JeremyProffittOrg/kb2040-single-key/BigSwitchCase.scad

// BigSwitchCase
// Case for the Kailh Big Switch / Adafruit KB2040 single-key build.
// Generated from the Tinkercad STL export (Big Switch Single Case part1);
// mesh translated to an OpenSCAD polyhedron.
// 4250 vertices, 8512 triangular faces.
// Units: millimetres.
//
// Side note: square openings on opposite outer walls are the tab-release
// access holes — insert a small flat screwdriver to push the switch tabs
// inward and free the Kailh Big Switch from the base.

module big_switch_case() {
    mesh_vertices = [
        [-68, 115.97, 36.107],
        [-68, 115.988, 36.136],
        [-68, 152.9, 1.625],
        [-68, 115.945, 36.08],
        [-68, 115.915, 36.056],
        [-68, 115.879, 36.036],
        [-68, 115.839, 36.019],
        [-68, 115.795, 36.007],
        [-68, 115.749, 36],
        [-68, 115.702, 35.998],
        [-68, 110.298, 35.998],
        [-68, 115.97, 39.893],
        [-68, 115.945, 39.92],
        [-68, 152.9, 63.375],
        [-68, 115.795, 39.993],
        [-68, 115.839, 39.981],
        [-68, 115.879, 39.964],
        [-68, 115.915, 39.944],
        [-68, 115.999, 39.834],
        [-68, 115.988, 39.864],
        [-68, 116.002, 39.802],
        [-65.913, 103.858, 45.729],
        [-65.859, 103.998, 45.796],
        [-65.852, 103.871, 45.796],
        [-65.888, 103.722, 45.729],
        [-65.83, 103.748, 45.796],
        [-65.859, 122.002, 45.796],
        [-65.921, 122.002, 45.729],
        [-65.921, 103.998, 45.729],
        [-65.957, 103.849, 45.657],
        [-65.966, 103.998, 45.657],
        [-65.931, 103.704, 45.657],
        [-65.984, 103.843, 45.581],
        [-65.993, 103.998, 45.581],
        [-65.957, 103.692, 45.581],
        [-65.993, 122.002, 45.581],
        [-65.966, 103.689, 45.502],
        [-65.993, 103.841, 45.502],
        [-66.224, 71.051, 1.371],
        [-66.541, 71.127, 1.371],
        [-66.212, 71.127, 1.123],
        [-28.702, 140, 4.998],
        [-23.298, 155, 4.998],
        [-28.702, 155, 4.998],
        [-68, 110.055, 39.92],
        [-68, 73.1, 63.375],
        [-68, 110.085, 39.944],
        [-68, 110.03, 39.893],
        [-68, 110.012, 39.864],
        [-68, 110.001, 39.834],
        [0.601999, 86.179, 3.038],
        [0.636999, 86.181, 3.038],
        [0.601999, 86.398, 2.998],
        [-68, 109.997, 39.802],
        [-68, 109.997, 36.198],
        [0.67, 86.189, 3.038],
        [0.702, 86.202, 3.038],
        [-68, 110.001, 36.166],
        [-68, 110.012, 36.136],
        [-68, 73.1, 1.625],
        [-68, 110.03, 36.107],
        [16, 110.251, 40],
        [16, 110.298, 40.003],
        [16, 73.1, 63.375],
        [16, 115.749, 40],
        [16, 152.9, 63.375],
        [16, 115.702, 40.003],
        [-68, 110.121, 36.036],
        [-68, 110.161, 36.019],
        [16, 115.795, 39.993],
        [-68, 110.251, 36],
        [-68, 110.121, 39.964],
        [-68, 110.161, 39.981],
        [-68, 110.205, 39.993],
        [-65.306, 122.451, 36.052],
        [-65.252, 122.456, 36.052],
        [-65.252, 122.59, 36.093],
        [-68, 110.205, 36.007],
        [-68, 110.085, 36.056],
        [-68, 110.055, 36.08],
        [-65.289, 122.308, 36.022],
        [-68, 110.251, 40],
        [16, 110.205, 36.007],
        [16, 73.1, 1.625],
        [16, 110.251, 36],
        [-65.324, 122.296, 36.022],
        [-65.358, 122.434, 36.052],
        [-29.003, 155, 5.198],
        [-29.003, 155, 8.802],
        [-29.003, 140, 8.802],
        [-65.252, 122.311, 36.022],
        [-65.493, 103.677, 45.948],
        [-65.416, 103.779, 45.978],
        [-65.452, 103.63, 45.948],
        [-35.5, 141.002, 39],
        [-16.5, 140.075, 39],
        [-16.5, 141.002, 39],
        [16, 115.988, 36.136],
        [16, 152.9, 1.625],
        [16, 115.999, 36.166],
        [16, 115.97, 36.107],
        [-65.564, 103.582, 45.907],
        [-65.528, 103.731, 45.948],
        [16, 115.945, 36.08],
        [16, 115.915, 36.056],
        [16, 115.879, 36.036],
        [-65.321, 122.583, 36.093],
        [0.601999, 141.002, 39.998],
        [-52.602, 141.002, 39.998],
        [-68, 115.702, 40.003],
        [16, 116.002, 36.198],
        [-35.5, 140.075, 39],
        [16, 115.988, 39.864],
        [16, 115.999, 39.834],
        [16, 116.002, 39.802],
        [16, 115.945, 39.92],
        [16, 115.915, 39.944],
        [16, 115.879, 39.964],
        [-65.609, 103.652, 45.907],
        [16, 115.839, 39.981],
        [-65.44, 103.816, 45.978],
        [16, 115.97, 39.893],
        [16, 110.03, 36.107],
        [16, 110.012, 36.136],
        [-66.517, 71.201, 1.123],
        [-66.478, 71.32, 0.887],
        [-66.193, 71.252, 0.887],
        [-65.389, 103.748, 45.978],
        [-65.407, 103.593, 45.948],
        [-66.807, 71.32, 1.123],
        [-16.273, 141.002, 38.896],
        [-16.345, 141.002, 38.954],
        [-16.422, 141.002, 38.988],
        [-65.556, 103.792, 45.948],
        [-65.645, 103.731, 45.907],
        [16, 110.298, 35.998],
        [16, 115.702, 35.998],
        [16, 115.749, 36],
        [16, 115.795, 36.007],
        [16, 115.839, 36.019],
        [13.757, 122.221, 36.144],
        [13.776, 122.113, 36.144],
        [13.852, 122.129, 36.204],
        [-65.681, 122.574, 36.204],
        [-65.645, 122.723, 36.271],
        [-65.725, 122.632, 36.271],
        [13.783, 122.002, 36.144],
        [13.688, 122.094, 36.093],
        [-16.345, 140.075, 38.954],
        [-16.273, 140.075, 38.896],
        [16, 110.055, 39.92],
        [16, 110.03, 39.893],
        [16, 110.205, 39.993],
        [16, 110.161, 39.981],
        [16, 110.121, 39.964],
        [16, 110.085, 39.944],
        [-66.166, 71.422, 0.67],
        [-65.9, 71.229, 0.887],
        [-16.054, 141.002, 38.481],
        [-16.095, 141.002, 38.608],
        [16, 109.997, 36.198],
        [-16.146, 141.002, 38.722],
        [-65.793, 122.526, 36.271],
        [-65.757, 122.675, 36.343],
        [-65.83, 122.561, 36.343],
        [13.859, 122.002, 36.204],
        [13.921, 122.002, 36.271],
        [13.912, 122.142, 36.271],
        [13.83, 122.252, 36.204],
        [0.731001, 86.22, 3.038],
        [0.757, 86.243, 3.038],
        [-65.672, 122.772, 36.343],
        [0.780001, 86.269, 3.038],
        [0.798, 86.298, 3.038],
        [0.811001, 86.33, 3.038],
        [0.819, 86.363, 3.038],
        [-65.347, 103.906, 45.996],
        [0.820999, 86.398, 3.038],
        [-65.289, 103.692, 45.978],
        [-65.324, 103.704, 45.978],
        [-65.289, 103.849, 45.996],
        [-65.9, 152.9, 65],
        [-64.199, 151.63, 65],
        [-63.938, 151.79, 65],
        [-65.776, 122.701, 36.419],
        [-65.852, 122.583, 36.419],
        [-64.431, 151.431, 65],
        [13.993, 122.002, 36.419],
        [13.957, 122.151, 36.343],
        [13.966, 122.002, 36.343],
        [-63.052, 152.003, 65],
        [-63.357, 151.978, 65],
        [-63.655, 151.907, 65],
        [-65.358, 103.722, 45.978],
        [-65.358, 103.566, 45.948],
        [-65.9, 155, 1.625],
        [-65.335, 103.887, 45.996],
        [-65.321, 103.871, 45.996],
        [0.799, 86.012, 3.158],
        [0.857, 86.048, 3.158],
        [13.725, 122.323, 36.144],
        [13.793, 122.37, 36.204],
        [0.908001, 86.092, 3.158],
        [-65.003, 75.948, 65],
        [-65.003, 150.052, 65],
        [-64.978, 150.357, 65],
        [-64.63, 151.199, 65],
        [-64.79, 150.938, 65],
        [-65.306, 103.858, 45.996],
        [-64.907, 150.655, 65],
        [-64.63, 74.801, 65],
        [-64.79, 75.062, 65],
        [-65.9, 73.1, 65],
        [13.848, 122.407, 36.271],
        [13.743, 122.478, 36.204],
        [-64.907, 75.345, 65],
        [-64.978, 75.643, 65],
        [-16.347, 140.071, 38.954],
        [-64.431, 74.569, 65],
        [-64.199, 74.37, 65],
        [-63.938, 74.21, 65],
        [0.67, 85.97, 3.158],
        [-63.655, 74.093, 65],
        [0.736, 85.986, 3.158],
        [-16.284, 140.064, 38.896],
        [-16.353, 140.068, 38.954],
        [-16.362, 140.064, 38.954],
        [-65.473, 103.902, 45.978],
        [-65.459, 103.857, 45.978],
        [-65.688, 122.802, 36.419],
        [-16.375, 140.061, 38.954],
        [-16.437, 140.068, 38.988],
        [-16.391, 140.059, 38.954],
        [-65.576, 103.857, 45.948],
        [13.888, 122.278, 36.271],
        [-65.593, 103.998, 45.948],
        [-65.589, 103.927, 45.948],
        [-65.688, 103.906, 45.907],
        [11.052, 73.997, 65],
        [-63.052, 73.997, 65],
        [13.9, 73.1, 65],
        [-16.422, 140.075, 38.988],
        [0.601999, 85.965, 3.158],
        [-63.357, 74.022, 65],
        [16, 110.012, 39.864],
        [16, 110.001, 39.834],
        [16, 110.001, 36.166],
        [16, 110.055, 36.08],
        [16, 110.121, 36.036],
        [16, 110.161, 36.019],
        [16, 110.085, 36.056],
        [-65.783, 122.71, 36.498],
        [-65.913, 122.451, 36.419],
        [-65.859, 122.59, 36.498],
        [13.931, 122.296, 36.343],
        [-65.484, 103.998, 45.978],
        [13.888, 122.434, 36.343],
        [0.799, 85.793, 3.354],
        [-16.464, 140.065, 38.988],
        [-16.476, 140.064, 38.988],
        [-16.43, 140.054, 38.954],
        [0.702, 85.77, 3.354],
        [0.891001, 85.831, 3.354],
        [-65.593, 122.893, 36.498],
        [-65.693, 122.811, 36.498],
        [-65.357, 103.927, 45.996],
        [16, 109.997, 39.802],
        [-16.423, 140.073, 38.988],
        [-16.43, 140.07, 38.988],
        [-36, 85.762, 3.354],
        [-36, 85.575, 3.623],
        [-36, 85.925, 3.19662],
        [-16.426, 140.071, 38.988],
        [-16.445, 140.067, 38.988],
        [-65.416, 122.675, 36.144],
        [-65.389, 122.561, 36.093],
        [-65.335, 122.701, 36.144],
        [-16.454, 140.066, 38.988],
        [-65.493, 122.632, 36.144],
        [-65.452, 122.526, 36.093],
        [0.601999, 85.762, 3.354],
        [-16.409, 140.056, 38.954],
        [-16.488, 140.063, 38.988],
        [-16.476, 140.052, 38.954],
        [-16.452, 140.053, 38.954],
        [-36, 85.15, 4.786],
        [-36, 85.265, 4.348],
        [-36, 85.408, 3.957],
        [-66.166, 154.578, 64.33],
        [-66.132, 154.367, 64.524],
        [-65.9, 154.385, 64.524],
        [-16.367, 140.047, 38.896],
        [-36, 84.997, 6.273],
        [-36, 85.015, 5.76],
        [-36, 85.066, 5.261],
        [-36, 85.925, 38.05],
        [-65.564, 122.574, 36.144],
        [-65.528, 122.723, 36.204],
        [-36, 84.997, 38.05],
        [-65.609, 122.657, 36.204],
        [-65.44, 122.772, 36.204],
        [0.976, 85.883, 3.354],
        [1.052, 85.948, 3.354],
        [1.117, 86.024, 3.354],
        [-65.556, 122.796, 36.271],
        [-16.339, 140.051, 38.896],
        [1.169, 86.109, 3.354],
        [0.952, 86.143, 3.158],
        [-65.347, 122.802, 36.204],
        [-16.146, 140.075, 38.722],
        [-16.206, 140.075, 38.819],
        [-16.21, 140.068, 38.819],
        [-16.276, 140.07, 38.896],
        [1.014, 86.264, 3.158],
        [1.23, 86.298, 3.354],
        [1.03, 86.33, 3.158],
        [1.238, 86.398, 3.354],
        [1.035, 86.398, 3.158],
        [-66.195, 153.807, 64.823],
        [-66.333, 153.749, 64.823],
        [-66.101, 153.517, 64.92],
        [-16.206, 141.002, 38.819],
        [-36, 141.002, 6.273],
        [-36, 140.075, 38.05],
        [-36, 141.002, 38.05],
        [-65.9, 154.134, 64.69],
        [-66.093, 154.119, 64.69],
        [-65.9, 153.853, 64.823],
        [-65.364, 103.949, 45.996],
        [-36, 140.075, 3.19662],
        [-16.151, 140.067, 38.722],
        [-36, 140.985, 5.76],
        [-16.22, 140.061, 38.819],
        [0.988001, 86.201, 3.158],
        [1.207, 86.201, 3.354],
        [-66.049, 153.842, 64.823],
        [-65.9, 153.549, 64.92],
        [-66.002, 153.541, 64.92],
        [12.199, 151.63, 65],
        [13.9, 152.9, 65],
        [11.938, 151.79, 65],
        [-66.281, 154.074, 64.69],
        [12.63, 151.199, 65],
        [12.431, 151.431, 65],
        [-36, 140.425, 3.623],
        [-36, 140.238, 3.354],
        [-36, 140.592, 3.957],
        [-36, 140.735, 4.348],
        [-36, 140.85, 4.786],
        [-36, 140.934, 5.261],
        [-16.185, 140.051, 38.722],
        [-16.115, 140.056, 38.608],
        [-16.164, 140.059, 38.722],
        [-16.214, 140.044, 38.722],
        [-16.14, 140.047, 38.608],
        [12.79, 150.938, 65],
        [13.003, 150.052, 65],
        [12.978, 150.357, 65],
        [12.907, 150.655, 65],
        [-65.9, 154.974, 63.629],
        [-65.9, 155, 63.375],
        [-66.229, 154.974, 63.375],
        [11.357, 151.978, 65],
        [11.655, 151.907, 65],
        [11.052, 152.003, 65],
        [-16.298, 140.06, 38.896],
        [13.984, 122.157, 36.419],
        [-29.003, 71, 5.198],
        [-65.9, 71, 1.625],
        [-28.999, 71, 5.166],
        [-16.316, 140.055, 38.896],
        [-28.988, 71, 5.136],
        [-28.97, 71, 5.107],
        [-28.879, 71, 5.036],
        [-28.915, 71, 5.056],
        [-28.795, 71, 5.007],
        [-28.839, 71, 5.019],
        [1.403, 85.816, 3.957],
        [1.268, 85.914, 3.623],
        [1.184, 85.816, 3.623],
        [-16.1, 140.066, 38.608],
        [13.957, 122.308, 36.419],
        [-28.879, 71, 8.964],
        [-65.9, 71, 63.375],
        [-28.915, 71, 8.944],
        [13.9, 71, 63.375],
        [-28.702, 71, 9.003],
        [13.912, 122.451, 36.419],
        [13.966, 122.311, 36.498],
        [13.921, 122.456, 36.498],
        [-28.749, 71, 9],
        [-28.97, 71, 8.893],
        [-28.945, 71, 8.92],
        [-28.795, 71, 8.993],
        [1.385, 86.143, 3.623],
        [-28.839, 71, 8.981],
        [1.415, 86.269, 3.623],
        [15.771, 153.853, 63.375],
        [15.873, 153.541, 63.629],
        [15.897, 153.549, 63.375],
        [-16.238, 140.055, 38.819],
        [-23.03, 71, 5.107],
        [13.9, 71, 1.625],
        [-23.012, 71, 5.136],
        [15.799, 153.517, 63.877],
        [15.748, 153.193, 64.113],
        [15.873, 153.212, 63.877],
        [-23.085, 71, 5.056],
        [-23.055, 71, 5.08],
        [13.993, 122.159, 36.498],
        [15.771, 152.9, 64.113],
        [15.897, 152.9, 63.877],
        [1.336, 86.024, 3.623],
        [-23.121, 71, 5.036],
        [-23.161, 71, 5.019],
        [-23.121, 71, 8.964],
        [-23.161, 71, 8.981],
        [15.949, 153.224, 63.629],
        [14.003, 122.002, 36.498],
        [15.974, 152.9, 63.629],
        [-22.998, 71, 8.802],
        [-23.001, 71, 8.834],
        [-23.03, 71, 8.893],
        [-23.055, 71, 8.92],
        [-23.085, 71, 8.944],
        [-23.205, 71, 8.993],
        [15.974, 153.229, 63.375],
        [1.086, 85.732, 3.623],
        [-23.298, 71, 9.003],
        [-23.251, 71, 9],
        [0.976, 85.664, 3.623],
        [1.184, 85.597, 3.957],
        [-28.945, 71, 5.08],
        [-28.749, 71, 5],
        [-28.702, 71, 4.998],
        [-23.298, 71, 4.998],
        [-23.205, 71, 5.007],
        [-23.251, 71, 5],
        [-23.001, 71, 5.166],
        [-16.327, 140.039, 38.819],
        [-23.012, 71, 8.864],
        [-22.998, 71, 5.198],
        [-16.262, 140.049, 38.819],
        [-16.292, 140.044, 38.819],
        [-65.576, 122.85, 36.343],
        [-29.003, 71, 8.802],
        [-28.999, 71, 8.834],
        [-28.988, 71, 8.864],
        [-65.459, 122.85, 36.271],
        [-65.252, 103.689, 45.978],
        [-65.271, 103.843, 45.996],
        [-65.252, 103.841, 45.996],
        [-16.43, 140.043, 38.896],
        [-16.464, 140.041, 38.896],
        [1.302, 85.698, 3.957],
        [-65.481, 103.949, 45.978],
        [-65.368, 103.973, 45.996],
        [-16.5, 140.031, 38.819],
        [-16.454, 140.031, 38.819],
        [13.252, 122.59, 36.093],
        [13.321, 122.583, 36.093],
        [13.335, 122.701, 36.144],
        [-65.473, 122.907, 36.343],
        [-16.397, 140.045, 38.896],
        [-65.589, 122.883, 36.419],
        [1.425, 86.398, 3.623],
        [13.252, 122.71, 36.144],
        [-16.367, 140.036, 38.819],
        [-16.292, 140.032, 38.722],
        [13.389, 122.561, 36.093],
        [13.452, 122.526, 36.093],
        [13.493, 122.632, 36.144],
        [13.416, 122.675, 36.144],
        [-16.409, 140.033, 38.819],
        [-65.364, 122.942, 36.343],
        [1.485, 85.948, 3.957],
        [1.544, 86.092, 3.957],
        [13.44, 122.772, 36.204],
        [-16.339, 140.028, 38.722],
        [1.58, 86.243, 3.957],
        [1.592, 86.398, 3.957],
        [-16.445, 140.023, 38.722],
        [-16.391, 140.025, 38.722],
        [-65.252, 103.998, 46.003],
        [12.431, 74.569, 65],
        [12.63, 74.801, 65],
        [12.79, 75.062, 65],
        [-65.357, 122.883, 36.271],
        [12.907, 75.345, 65],
        [13.003, 75.948, 65],
        [12.978, 75.643, 65],
        [-16.25, 140.037, 38.722],
        [-65.252, 122.71, 36.144],
        [-65.252, 122.811, 36.204],
        [-65.252, 122.954, 36.343],
        [1.721, 86.22, 4.348],
        [-65.252, 122.893, 36.271],
        [11.357, 74.022, 65],
        [11.655, 74.093, 65],
        [1.735, 86.398, 4.348],
        [-16.316, 140.021, 38.608],
        [11.938, 74.21, 65],
        [12.199, 74.37, 65],
        [-65.481, 122.942, 36.419],
        [-16.173, 140.039, 38.608],
        [-16.214, 140.032, 38.608],
        [1.519, 85.732, 4.348],
        [1.612, 85.883, 4.348],
        [-65.252, 122.99, 36.419],
        [1.68, 86.048, 4.348],
        [-16.262, 140.026, 38.608],
        [1.835, 86.202, 4.786],
        [1.789, 86.012, 4.786],
        [-16.095, 140.075, 38.608],
        [1.85, 86.398, 4.786],
        [-65.37, 122.99, 36.498],
        [-65.484, 122.954, 36.498],
        [-16.06, 140.065, 38.481],
        [-16.054, 140.075, 38.481],
        [-65.37, 103.998, 45.996],
        [13.252, 122.811, 36.204],
        [13.357, 122.883, 36.271],
        [13.252, 122.893, 36.271],
        [1.612, 85.664, 4.786],
        [1.714, 85.831, 4.786],
        [1.789, 85.793, 5.261],
        [-16.14, 140.036, 38.481],
        [-65.003, 103.841, 45.996],
        [-65.003, 103.689, 45.978],
        [-65.003, 103.544, 45.948],
        [15.799, 72.483, 63.877],
        [15.873, 72.459, 63.629],
        [15.949, 72.776, 63.629],
        [13.459, 122.85, 36.271],
        [13.347, 122.802, 36.204],
        [-16.185, 140.028, 38.481],
        [15.873, 72.788, 63.877],
        [15.974, 73.1, 63.629],
        [15.897, 73.1, 63.877],
        [-66.193, 153.049, 64.98],
        [-66.212, 153.002, 64.98],
        [15.974, 72.771, 63.375],
        [13.364, 122.942, 36.343],
        [1.869, 85.986, 5.261],
        [1.968, 86.181, 5.76],
        [1.918, 86.189, 5.261],
        [1.985, 86.398, 5.76],
        [1.934, 86.398, 5.261],
        [-66.093, 153.166, 64.98],
        [-66.132, 153.132, 64.98],
        [-66.049, 153.193, 64.98],
        [-66.002, 153.212, 64.98],
        [-65.951, 153.224, 64.98],
        [-65.9, 153.229, 64.98],
        [13.252, 122.954, 36.343],
        [-65.003, 103.998, 46.003],
        [13.252, 122.99, 36.419],
        [13.368, 122.978, 36.419],
        [1.68, 85.615, 5.261],
        [1.835, 85.77, 5.76],
        [15.897, 72.451, 63.375],
        [13.473, 122.907, 36.343],
        [13.576, 122.85, 36.343],
        [1.918, 85.97, 5.76],
        [-66.224, 152.951, 64.98],
        [-66.229, 152.9, 64.98],
        [-65.783, 103.998, 45.856],
        [13.564, 122.574, 36.144],
        [13.681, 122.574, 36.204],
        [13.609, 122.657, 36.204],
        [13.528, 122.723, 36.204],
        [15.974, 153.229, 1.625],
        [15.897, 153.549, 1.625],
        [15.974, 72.771, 1.625],
        [-66.281, 153.425, 64.92],
        [-16.076, 140.054, 38.481],
        [-16.103, 140.045, 38.481],
        [-65.368, 122.978, 36.419],
        [15.074, 154.516, 63.877],
        [14.807, 154.68, 63.877],
        [15, 154.414, 64.113],
        [-65.003, 102.997, 41.548],
        [-65.252, 102.997, 45.502],
        [-65.003, 102.997, 45.502],
        [13.645, 122.723, 36.271],
        [-64.978, 102.997, 41.305],
        [-65.252, 102.997, 36.498],
        [14.749, 154.567, 64.113],
        [14.899, 154.274, 64.33],
        [-63.938, 151.79, 41.548],
        [13.627, 122.502, 36.144],
        [-67.974, 73.1, 1.371],
        [-16.115, 140.033, 38.344],
        [15.367, 154.367, 63.629],
        [15.119, 154.578, 63.629],
        [15.312, 154.312, 63.877],
        [14.842, 72.951, 64.823],
        [15.119, 72.907, 64.69],
        [15.134, 73.1, 64.69],
        [-54.003, 122.99, 36.419],
        [-65.252, 123.002, 36.498],
        [14.853, 73.1, 64.823],
        [-54.003, 122.954, 36.343],
        [-66.003, 103.998, 36.498],
        [-66.003, 110.001, 39.834],
        [-66.003, 103.998, 45.502],
        [-66.003, 110.012, 39.864],
        [-66.003, 109.997, 39.802],
        [-66.003, 109.997, 36.498],
        [-65.859, 122.59, 45.502],
        [-16.437, 140.015, 38.608],
        [-16.375, 140.017, 38.608],
        [-16.024, 140.075, 38.344],
        [-54.003, 122.893, 36.271],
        [15.367, 72.868, 64.524],
        [15.599, 73.1, 64.33],
        [15.385, 73.1, 64.524],
        [-16.048, 140.053, 38.344],
        [14.842, 154.748, 63.629],
        [-16.076, 140.043, 38.344],
        [-53.117, 85.388, 4.348],
        [-53.052, 85.515, 3.957],
        [-53.184, 85.597, 3.957],
        [14.807, 72.805, 64.823],
        [15.074, 72.719, 64.69],
        [14.749, 72.667, 64.823],
        [15, 72.54, 64.69],
        [15.223, 72.426, 64.524],
        [15.312, 72.641, 64.524],
        [-16.298, 140.015, 38.481],
        [-66.003, 122.002, 36.498],
        [-65.993, 122.159, 45.502],
        [-66.003, 122.002, 45.502],
        [14.899, 72.374, 64.69],
        [-65.693, 122.811, 45.502],
        [-65.783, 122.71, 45.502],
        [-16.238, 140.021, 38.481],
        [15.516, 72.575, 64.33],
        [-16.284, 140.011, 38.344],
        [-16.362, 140.011, 38.481],
        [-16.43, 140.009, 38.481],
        [-65.252, 123.002, 45.502],
        [-65.37, 122.99, 45.502],
        [-53.086, 85.732, 3.623],
        [-52.908, 85.456, 3.957],
        [-52.976, 85.664, 3.623],
        [1.85, 85.762, 6.273],
        [1.934, 85.965, 6.273],
        [-16.22, 140.017, 38.344],
        [-52.757, 85.42, 3.957],
        [-52.857, 85.615, 3.623],
        [15.578, 72.834, 64.33],
        [1.985, 86.179, 6.273],
        [2.003, 86.398, 6.273],
        [15.68, 72.522, 64.113],
        [15.414, 72.329, 64.33],
        [-52.78, 85.279, 4.348],
        [-16.164, 140.025, 38.344],
        [-65.913, 122.142, 45.729],
        [-65.966, 122.002, 45.657],
        [-65.957, 122.151, 45.657],
        [-16.5, 140.014, 38.608],
        [-16.5, 140.008, 38.481],
        [-16.5, 140.022, 38.722],
        [1.985, 139.602, 5.76],
        [-52.602, 85.408, 3.957],
        [-52.731, 85.585, 3.623],
        [-52.602, 85.575, 3.623],
        [15.748, 72.807, 64.113],
        [1.721, 85.585, 5.76],
        [1.735, 85.575, 6.273],
        [13.556, 122.796, 36.271],
        [13.672, 122.772, 36.343],
        [13.757, 122.675, 36.343],
        [-65.776, 122.113, 45.856],
        [-65.852, 122.129, 45.796],
        [-65.783, 122.002, 45.856],
        [-16.006, 140.075, 38.199],
        [-16.024, 141.002, 38.344],
        [1.592, 85.408, 6.273],
        [1.592, 85.408, 39.998],
        [1.735, 85.575, 39.998],
        [1.934, 85.965, 39.998],
        [-52.602, 85.265, 4.348],
        [1.985, 86.179, 39.998],
        [2.003, 86.398, 39.998],
        [2.003, 102.997, 27.0025],
        [-52.952, 85.32, 4.348],
        [-16.03, 140.064, 38.344],
        [13.589, 122.883, 36.419],
        [1.85, 85.762, 39.998],
        [-16.1, 140.031, 38.199],
        [13.481, 122.942, 36.419],
        [-65.252, 122.159, 45.996],
        [-65.252, 122.002, 46.003],
        [-65.271, 122.157, 45.996],
        [13.37, 122.99, 36.498],
        [13.484, 122.954, 36.498],
        [-65.321, 122.129, 45.996],
        [-65.335, 122.113, 45.996],
        [13.252, 123.002, 36.498],
        [-65.347, 122.094, 45.996],
        [-65.357, 122.073, 45.996],
        [-53.268, 85.481, 4.348],
        [2.003, 123.002, 36.498],
        [2.003, 122.99, 36.419],
        [4.003, 102.997, 30],
        [2.003, 102.997, 32.9985],
        [-53.169, 85.286, 4.786],
        [-53.336, 85.388, 4.786],
        [-16.06, 140.041, 38.199],
        [-16.03, 140.052, 38.199],
        [13.593, 122.893, 36.498],
        [-16, 84.997, 6.273],
        [-16, 85.925, 38.05],
        [-16, 84.997, 38.05],
        [-16.151, 140.023, 38.199],
        [-16.21, 140.015, 38.199],
        [0.601999, 84.997, 39.998],
        [0.601999, 84.997, 6.273],
        [-65.921, 122.456, 45.502],
        [-65.921, 122.456, 36.498],
        [-16.012, 140.063, 38.199],
        [-65.966, 122.311, 45.502],
        [-16.095, 140.031, 38.05],
        [-53.403, 85.597, 4.348],
        [-65.984, 122.157, 45.581],
        [13.783, 122.71, 36.498],
        [13.693, 122.811, 36.498],
        [13.688, 122.802, 36.419],
        [-16.006, 141.002, 38.199],
        [-52.988, 85.211, 4.786],
        [-16.353, 140.007, 38.344],
        [-16.426, 140.005, 38.344],
        [-16, 85.015, 5.76],
        [-16, 85.925, 3.19662],
        [-53.519, 85.732, 4.348],
        [-53.485, 85.515, 4.786],
        [13.725, 122.632, 36.271],
        [-16.024, 140.052, 38.05],
        [-53.612, 85.664, 4.786],
        [-53.544, 85.456, 5.261],
        [-16.054, 140.041, 38.05],
        [-65.931, 122.296, 45.657],
        [-16.423, 140.002, 38.199],
        [-16.347, 140.005, 38.199],
        [-52.602, 85.15, 4.786],
        [-52.602, 86.398, 2.998],
        [-52.602, 86.179, 3.038],
        [-35.5, 86, 3.13837],
        [-16.5, 86, 3.13837],
        [-16.422, 85.999, 3.13893],
        [-16, 85.762, 3.354],
        [-16, 85.575, 3.623],
        [-16, 85.408, 3.957],
        [-65.83, 122.252, 45.796],
        [-65.888, 122.278, 45.729],
        [-16, 85.265, 4.348],
        [-16, 85.15, 4.786],
        [-16, 85.066, 5.261],
        [13.793, 122.526, 36.271],
        [13.83, 122.561, 36.343],
        [-16.276, 140.009, 38.199],
        [-52.798, 85.165, 4.786],
        [-16.006, 140.063, 38.05],
        [13.852, 122.583, 36.419],
        [13.776, 122.701, 36.419],
        [-16.146, 140.022, 38.05],
        [-16.206, 140.014, 38.05],
        [-65.757, 122.221, 45.856],
        [13.859, 122.59, 36.498],
        [-52.811, 85.082, 5.261],
        [-53.014, 85.131, 5.261],
        [-52.819, 85.032, 5.76],
        [15.771, 73.1, 64.113],
        [-65.688, 122.094, 45.907],
        [-65.693, 122.002, 45.907],
        [-65.725, 122.323, 45.856],
        [-65.645, 122.269, 45.907],
        [14.549, 154.897, 63.375],
        [14.853, 154.771, 63.375],
        [-16, 140.075, 38.05],
        [-53.207, 85.211, 5.261],
        [13.693, 122.811, 45.502],
        [-53.385, 85.32, 5.261],
        [14.95, 153.95, 64.524],
        [14.773, 154.101, 64.524],
        [14.773, 153.773, 64.69],
        [-65.672, 122.184, 45.907],
        [15.567, 72.251, 64.113],
        [15.68, 72.193, 63.877],
        [12.199, 123.002, 40.294],
        [11.938, 123.002, 40.166],
        [12.79, 123.002, 40.844],
        [12.63, 123.002, 40.636],
        [-65.957, 122.308, 45.581],
        [15, 153.46, 64.69],
        [14.899, 153.626, 64.69],
        [14.749, 153.333, 64.823],
        [2.003, 123.002, 39.998],
        [11.052, 123.002, 39.998],
        [11.357, 123.002, 40.017],
        [14.224, 73.049, 64.98],
        [14.541, 72.998, 64.92],
        [14.549, 73.1, 64.92],
        [-53.714, 85.831, 4.786],
        [-53.68, 85.615, 5.261],
        [15.101, 153.773, 64.524],
        [15.101, 154.101, 64.33],
        [14.166, 72.907, 64.98],
        [14.193, 72.951, 64.98],
        [-65.83, 122.561, 45.657],
        [-65.888, 122.434, 45.657],
        [-65.913, 122.451, 45.581],
        [14.132, 72.868, 64.98],
        [14.093, 72.834, 64.98],
        [-65.852, 122.583, 45.581],
        [14.003, 116.002, 39.802],
        [14.003, 115.999, 39.834],
        [14.002, 72.788, 64.98],
        [13.951, 72.776, 64.98],
        [14.003, 116.002, 36.498],
        [14.517, 72.899, 64.92],
        [11.655, 123.002, 40.073],
        [14.212, 72.998, 64.98],
        [-53.03, 85.082, 5.76],
        [14.478, 72.805, 64.92],
        [-65.848, 122.407, 45.729],
        [-53.23, 85.165, 5.76],
        [-53.035, 85.066, 6.273],
        [14.229, 73.1, 64.98],
        [-28.879, 86, 8.964],
        [-28.915, 86, 8.944],
        [-35.5, 86, 38.05],
        [-28.945, 86, 8.92],
        [-53.721, 85.585, 5.76],
        [-53.58, 85.42, 5.76],
        [-28.97, 86, 8.893],
        [-28.988, 86, 8.864],
        [-28.999, 86, 8.834],
        [-29.003, 86, 8.802],
        [-53.415, 85.279, 5.76],
        [-28.999, 86, 5.166],
        [-28.988, 86, 5.136],
        [-28.879, 86, 5.036],
        [-28.915, 86, 5.056],
        [-65.793, 122.526, 45.729],
        [14.425, 72.719, 64.92],
        [13.252, 110.298, 35.998],
        [13.252, 115.702, 35.998],
        [-22.998, 86, 5.198],
        [-23.001, 86, 5.166],
        [-52.602, 84.997, 6.273],
        [-52.821, 85.015, 6.273],
        [-23.03, 86, 5.107],
        [-23.055, 86, 5.08],
        [-23.205, 86, 5.007],
        [-23.161, 86, 5.019],
        [-23.085, 86, 5.056],
        [-23.121, 86, 5.036],
        [-65.743, 122.478, 45.796],
        [-28.795, 86, 8.993],
        [-28.839, 86, 8.981],
        [-28.749, 86, 9],
        [-16.5, 86, 38.05],
        [-28.702, 86, 9.003],
        [-23.298, 86, 9.003],
        [-23.251, 86, 9],
        [-52.602, 85.015, 5.76],
        [-52.602, 85.066, 5.261],
        [-23.205, 86, 8.993],
        [-65.793, 122.37, 45.796],
        [-23.03, 86, 8.893],
        [-23.055, 86, 8.92],
        [-23.161, 86, 8.981],
        [-23.121, 86, 8.964],
        [-23.085, 86, 8.944],
        [-28.945, 86, 5.08],
        [-28.97, 86, 5.107],
        [14.359, 72.641, 64.92],
        [14.281, 72.575, 64.92],
        [14.574, 72.426, 64.823],
        [14.46, 72.329, 64.823],
        [-23.012, 86, 8.864],
        [-23.001, 86, 8.834],
        [-22.998, 86, 8.802],
        [-23.012, 86, 5.136],
        [2.003, 122.002, 35.998],
        [13.252, 122.002, 35.998],
        [14.671, 72.54, 64.823],
        [-29.003, 86, 5.198],
        [-28.702, 86, 4.998],
        [-23.251, 86, 5],
        [-23.298, 86, 4.998],
        [-28.749, 86, 5],
        [-28.795, 86, 5.007],
        [-28.839, 86, 5.019],
        [-63.357, 151.978, 41.548],
        [-65.681, 122.418, 45.856],
        [-16.5, 84.997, 39],
        [-35.5, 84.997, 39],
        [-52.602, 84.997, 39.998],
        [-66.425, 154.516, 64.33],
        [-66.671, 154.414, 64.33],
        [-66.359, 154.312, 64.524],
        [13.9, 72.771, 64.98],
        [14.002, 72.459, 64.92],
        [14.049, 72.807, 64.98],
        [15.074, 153.281, 64.69],
        [15.223, 153.574, 64.524],
        [-65.9, 154.599, 64.33],
        [15.312, 153.359, 64.524],
        [-65.627, 122.502, 45.856],
        [14.195, 72.522, 64.92],
        [-53.425, 85.265, 6.273],
        [-53.238, 85.15, 6.273],
        [-65.9, 154.771, 64.113],
        [-66.193, 154.748, 64.113],
        [-53.425, 85.265, 39.998],
        [-53.592, 85.408, 6.273],
        [-53.238, 85.15, 39.998],
        [14.101, 72.483, 64.92],
        [-66.749, 154.567, 64.113],
        [-66.478, 154.68, 64.113],
        [13.9, 72.451, 64.92],
        [-16.273, 140.008, 38.05],
        [-16.422, 140.001, 38.05],
        [-16.345, 140.004, 38.05],
        [-67, 154.414, 64.113],
        [-53.735, 85.575, 6.273],
        [-66.899, 154.274, 64.33],
        [-16.5, 85.925, 39],
        [-16, 141.002, 38.05],
        [-35.5, 85.925, 39],
        [-16.5, 140.001, 38.199],
        [-67.074, 154.516, 63.877],
        [15.274, 153.899, 64.33],
        [-16.5, 140.004, 38.344],
        [-66.807, 154.68, 63.877],
        [-16.284, 85.936, 38.896],
        [-16.298, 85.94, 38.896],
        [-16.353, 85.932, 38.954],
        [-66.517, 154.799, 63.877],
        [-16.347, 85.929, 38.954],
        [-16.345, 85.925, 38.954],
        [-16.276, 85.93, 38.896],
        [-16.273, 85.925, 38.896],
        [-16.316, 85.945, 38.896],
        [-16.362, 85.936, 38.954],
        [-66.212, 154.873, 63.877],
        [-65.9, 154.897, 63.877],
        [-16.423, 85.927, 38.988],
        [-16.422, 85.925, 38.988],
        [-16.422, 84.997, 38.988],
        [-16.5, 140, 38.05],
        [-66.842, 154.748, 63.629],
        [-66.541, 154.873, 63.629],
        [-66.224, 154.949, 63.629],
        [15.414, 153.671, 64.33],
        [15.414, 154, 64.113],
        [-16.375, 85.939, 38.954],
        [-16.206, 140.014, 3.14622],
        [15.223, 154.223, 64.113],
        [-67.119, 154.578, 63.629],
        [-16.426, 85.929, 38.988],
        [-16.464, 85.935, 38.988],
        [-16.476, 85.936, 38.988],
        [-16.488, 85.937, 38.988],
        [-35.5, 140.014, 38.608],
        [-16.454, 85.934, 38.988],
        [-67.134, 154.599, 63.375],
        [-66.549, 154.897, 63.375],
        [-35.536, 140.041, 38.896],
        [-67.367, 154.367, 63.629],
        [-35.512, 140.063, 38.988],
        [-66.46, 154, 64.69],
        [-16.43, 85.93, 38.988],
        [15.516, 153.425, 64.33],
        [15.567, 153.749, 64.113],
        [15.68, 153.478, 64.113],
        [-16.391, 85.941, 38.954],
        [-16.437, 85.932, 38.988],
        [15.516, 154.074, 63.877],
        [-16.452, 85.947, 38.954],
        [-16.476, 85.948, 38.954],
        [-16.43, 85.946, 38.954],
        [-35.546, 140.031, 38.819],
        [-35.5, 140.022, 38.722],
        [-66.574, 154.223, 64.524],
        [-35.5, 140.004, 38.344],
        [-16.445, 85.933, 38.988],
        [-16.409, 85.944, 38.954],
        [-66.95, 153.95, 64.524],
        [-67.101, 153.773, 64.524],
        [-66.773, 153.773, 64.69],
        [-66.773, 154.101, 64.524],
        [-66.626, 153.899, 64.69],
        [15.68, 153.807, 63.877],
        [-16.397, 85.955, 38.896],
        [15.748, 153.842, 63.629],
        [15.578, 154.119, 63.629],
        [-67.274, 153.899, 64.33],
        [14.195, 72.193, 64.823],
        [-16.43, 85.957, 38.896],
        [14.049, 72.158, 64.823],
        [15.101, 72.227, 64.524],
        [-16.21, 85.932, 38.819],
        [-16.164, 85.941, 38.722],
        [-16.22, 85.939, 38.819],
        [14.132, 154.367, 64.524],
        [13.9, 154.599, 64.33],
        [13.9, 154.385, 64.524],
        [14.773, 72.227, 64.69],
        [-66.574, 153.574, 64.823],
        [-66.359, 153.359, 64.92],
        [14.95, 72.05, 64.524],
        [15.385, 154.385, 63.375],
        [-66.195, 153.478, 64.92],
        [-16.185, 85.949, 38.722],
        [-66.46, 153.671, 64.823],
        [14.773, 71.899, 64.524],
        [14.899, 71.726, 64.33],
        [15.101, 71.899, 64.33],
        [14.671, 154.414, 64.33],
        [-16.151, 85.933, 38.722],
        [-16.206, 85.925, 38.819],
        [15.274, 72.101, 64.33],
        [-16.146, 85.925, 38.722],
        [-16.146, 84.997, 38.722],
        [14.166, 154.578, 64.33],
        [-16.214, 85.956, 38.722],
        [-16.173, 85.961, 38.608],
        [-16.14, 85.953, 38.608],
        [-16.095, 85.925, 38.608],
        [-16.1, 85.934, 38.608],
        [15.414, 72, 64.113],
        [15.223, 71.777, 64.113],
        [-66.899, 153.626, 64.69],
        [-67, 153.46, 64.69],
        [-66.671, 153.46, 64.823],
        [-65.576, 122.143, 45.948],
        [-65.589, 122.073, 45.948],
        [15, 71.586, 64.113],
        [-16.273, 84.997, 38.896],
        [-66.749, 153.333, 64.823],
        [-66.425, 153.281, 64.92],
        [-65.564, 122.418, 45.907],
        [-16.214, 85.968, 38.608],
        [-65.481, 122.051, 45.978],
        [-65.473, 122.098, 45.978],
        [-67.223, 153.574, 64.524],
        [15.516, 71.926, 63.877],
        [-65.593, 122.002, 45.948],
        [-67.074, 153.281, 64.69],
        [-16.339, 85.949, 38.896],
        [15.074, 71.484, 63.877],
        [15.367, 71.633, 63.629],
        [15.312, 71.688, 63.877],
        [-65.368, 122.027, 45.996],
        [-65.484, 122.002, 45.978],
        [-16.292, 85.956, 38.819],
        [-16.327, 85.961, 38.819],
        [14.749, 71.433, 64.113],
        [-16.262, 85.951, 38.819],
        [14.807, 71.32, 63.877],
        [15.119, 71.422, 63.629],
        [-67.312, 153.359, 64.524],
        [-52.891, 85.831, 3.354],
        [14.425, 154.516, 64.33],
        [14.193, 154.748, 64.113],
        [-65.459, 122.143, 45.978],
        [14.478, 154.68, 64.113],
        [-16.238, 85.945, 38.819],
        [-67.101, 154.101, 64.33],
        [-65.364, 122.051, 45.996],
        [14.359, 154.312, 64.524],
        [-67.312, 154.312, 63.877],
        [-67.223, 154.223, 64.113],
        [15.578, 71.881, 63.629],
        [14.842, 71.252, 63.629],
        [-65.556, 122.208, 45.948],
        [-16.367, 85.953, 38.896],
        [14.517, 154.799, 63.877],
        [15.748, 72.158, 63.629],
        [13.9, 154.771, 64.113],
        [-67.385, 154.385, 63.375],
        [-67.414, 153.671, 64.33],
        [-67.516, 153.425, 64.33],
        [14.212, 154.873, 63.877],
        [-16.464, 85.959, 38.896],
        [13.9, 154.897, 63.877],
        [15.599, 71.866, 63.375],
        [15.385, 71.615, 63.375],
        [-16.367, 85.964, 38.819],
        [-16.409, 85.967, 38.819],
        [-67.414, 154, 64.113],
        [14.333, 72.251, 64.823],
        [14.626, 72.101, 64.69],
        [14.541, 154.873, 63.629],
        [14.224, 154.949, 63.629],
        [13.9, 154.974, 63.629],
        [-67.578, 153.166, 64.33],
        [-16.454, 85.969, 38.819],
        [-67.567, 153.749, 64.113],
        [-67.68, 153.478, 64.113],
        [-16.445, 85.977, 38.722],
        [-65.44, 122.184, 45.978],
        [-65.528, 122.269, 45.948],
        [-65.416, 122.221, 45.978],
        [-16.339, 85.972, 38.722],
        [14.46, 72, 64.69],
        [-67.799, 153.517, 63.877],
        [-16.25, 85.962, 38.722],
        [-65.389, 122.252, 45.978],
        [14.626, 153.899, 64.69],
        [14.574, 153.574, 64.823],
        [-67.516, 154.074, 63.877],
        [-16.391, 85.975, 38.722],
        [14.574, 71.777, 64.524],
        [14.229, 154.974, 63.375],
        [-67.68, 153.807, 63.877],
        [13.9, 72.147, 64.823],
        [13.9, 71.866, 64.69],
        [14.093, 71.881, 64.69],
        [-16.292, 85.968, 38.722],
        [-16.316, 85.979, 38.608],
        [14.574, 154.223, 64.524],
        [14.46, 154, 64.69],
        [-65.37, 122.002, 45.996],
        [-67.578, 154.119, 63.629],
        [-67.748, 153.842, 63.629],
        [14.281, 154.074, 64.69],
        [14.281, 71.926, 64.69],
        [14.359, 71.688, 64.524],
        [-67.599, 154.134, 63.375],
        [-16.345, 84.997, 38.954],
        [14.093, 154.119, 64.69],
        [14.049, 153.842, 64.823],
        [14.195, 153.807, 64.823],
        [-16.437, 85.985, 38.608],
        [14.132, 71.633, 64.524],
        [13.9, 71.615, 64.524],
        [-67.873, 153.541, 63.629],
        [-67.949, 153.224, 63.629],
        [-16.115, 85.944, 38.608],
        [13.9, 154.134, 64.69],
        [-67.897, 153.549, 63.375],
        [-67.974, 153.229, 63.375],
        [13.9, 153.853, 64.823],
        [-67.771, 153.853, 63.375],
        [-67.599, 154.134, 1.625],
        [14.425, 71.484, 64.33],
        [14.671, 71.586, 64.33],
        [14.166, 71.422, 64.33],
        [-65.306, 122.142, 45.996],
        [-16.06, 85.935, 38.481],
        [13.9, 71.401, 64.33],
        [-66.229, 154.974, 1.625],
        [-66.853, 154.771, 63.375],
        [14.478, 71.32, 64.113],
        [14.193, 71.252, 64.113],
        [14.46, 153.671, 64.823],
        [14.333, 153.749, 64.823],
        [14.281, 153.425, 64.92],
        [14.359, 153.359, 64.92],
        [14.425, 153.281, 64.92],
        [-67.134, 154.599, 1.625],
        [14.671, 153.46, 64.823],
        [13.9, 71.229, 64.113],
        [14.212, 71.127, 63.877],
        [-66.166, 153.093, 64.98],
        [14.195, 153.478, 64.92],
        [-66.517, 153.101, 64.92],
        [-66.541, 153.002, 64.92],
        [13.9, 71.103, 63.877],
        [13.9, 71.026, 63.629],
        [14.224, 71.051, 63.629],
        [14.517, 71.201, 63.877],
        [-66.478, 153.195, 64.92],
        [14.541, 71.127, 63.629],
        [14.002, 153.541, 64.92],
        [14.101, 153.517, 64.92],
        [-16.103, 85.955, 38.481],
        [-16.076, 85.946, 38.481],
        [-66.549, 152.9, 64.92],
        [-16.076, 85.957, 38.344],
        [15.599, 154.134, 63.375],
        [15.134, 71.401, 1.625],
        [15.385, 71.615, 1.625],
        [15.134, 71.401, 63.375],
        [-65.289, 122.151, 45.996],
        [14.853, 71.229, 63.375],
        [-16.054, 85.925, 38.481],
        [13.9, 153.549, 64.92],
        [-65.564, 122.574, 45.856],
        [-65.511, 122.478, 45.907],
        [-16.054, 84.997, 38.481],
        [-16.024, 85.925, 38.344],
        [-65.681, 122.574, 45.796],
        [-16.185, 85.972, 38.481],
        [-16.238, 85.979, 38.481],
        [-16.14, 85.964, 38.481],
        [15.134, 154.599, 63.375],
        [15.771, 72.147, 63.375],
        [-65.493, 122.323, 45.948],
        [-65.609, 122.348, 45.907],
        [15.599, 154.134, 1.625],
        [14.549, 71.103, 63.375],
        [-16.048, 85.947, 38.344],
        [13.9, 155, 63.375],
        [14.229, 71.026, 63.375],
        [-16.5, 85.986, 38.608],
        [-66.807, 153.195, 64.823],
        [-66.842, 153.049, 64.823],
        [-16.375, 85.983, 38.608],
        [-66.853, 152.9, 64.823],
        [-16.262, 85.974, 38.608],
        [-52.976, 85.883, 3.354],
        [-53.052, 85.948, 3.354],
        [-65.452, 122.37, 45.948],
        [-67.119, 153.093, 64.69],
        [-52.857, 86.048, 3.158],
        [-35.727, 141.002, 38.896],
        [-35.794, 141.002, 38.819],
        [-16.298, 85.985, 38.481],
        [-16.362, 85.989, 38.481],
        [-35.655, 141.002, 38.954],
        [-67.134, 152.9, 64.69],
        [-35.578, 141.002, 38.988],
        [-35.5, 140.001, 38.199],
        [-53.117, 86.024, 3.354],
        [-52.952, 86.143, 3.158],
        [-52.988, 86.201, 3.158],
        [-53.169, 86.109, 3.354],
        [-52.908, 86.092, 3.158],
        [-66.229, 73.1, 64.98],
        [-67.385, 152.9, 64.524],
        [-67.367, 153.132, 64.524],
        [-65.407, 122.407, 45.948],
        [-35.854, 141.002, 38.722],
        [-67.748, 153.193, 64.113],
        [-67.599, 152.9, 64.33],
        [-35.536, 140.065, 38.988],
        [-35.524, 140.064, 38.988],
        [-35.546, 140.066, 38.988],
        [-35.555, 140.067, 38.988],
        [-35.574, 140.071, 38.988],
        [-35.57, 140.07, 38.988],
        [-35.727, 140.075, 38.896],
        [-35.655, 140.075, 38.954],
        [-67.873, 153.212, 63.877],
        [-67.974, 152.9, 63.629],
        [-67.897, 152.9, 63.877],
        [-53.035, 86.398, 3.158],
        [-53.23, 86.298, 3.354],
        [-53.03, 86.33, 3.158],
        [-35.524, 140.052, 38.954],
        [-35.548, 140.053, 38.954],
        [0.601999, 139.602, 2.998],
        [0.820999, 139.602, 3.038],
        [0.819, 139.637, 3.038],
        [-53.207, 86.201, 3.354],
        [0.811001, 139.67, 3.038],
        [-67.771, 152.9, 64.113],
        [-35.563, 140.068, 38.988],
        [-53.014, 86.264, 3.158],
        [-52.798, 86.298, 3.038],
        [-35.577, 140.073, 38.988],
        [-35.578, 140.075, 38.988],
        [-52.78, 86.269, 3.038],
        [-53.238, 86.398, 3.354],
        [-67.771, 153.853, 1.625],
        [-35.638, 140.064, 38.954],
        [0.757, 139.757, 3.038],
        [0.731001, 139.78, 3.038],
        [-35.625, 140.061, 38.954],
        [-35.609, 140.059, 38.954],
        [0.702, 139.798, 3.038],
        [-35.647, 140.068, 38.954],
        [-52.821, 86.398, 3.038],
        [-52.819, 86.363, 3.038],
        [0.67, 139.811, 3.038],
        [-35.653, 140.071, 38.954],
        [0.636999, 139.819, 3.038],
        [0.601999, 139.821, 3.038],
        [-35.57, 140.054, 38.954],
        [14.853, 152.9, 64.823],
        [15.134, 152.9, 64.69],
        [15.119, 153.093, 64.69],
        [-16.22, 85.983, 38.344],
        [-35.591, 140.056, 38.954],
        [-16.43, 85.991, 38.481],
        [-66.549, 73.1, 64.92],
        [0.798, 139.702, 3.038],
        [0.780001, 139.731, 3.038],
        [-16.5, 85.978, 38.722],
        [15.367, 153.132, 64.524],
        [15.385, 152.9, 64.524],
        [14.807, 153.195, 64.823],
        [-35.661, 140.051, 38.896],
        [-35.633, 140.047, 38.896],
        [14.842, 153.049, 64.823],
        [-67.974, 153.229, 1.625],
        [15.578, 153.166, 64.33],
        [-64.199, 150.052, 40.294],
        [-64.414, 150.268, 40.452],
        [-64.431, 150.052, 40.452],
        [15.599, 152.9, 64.33],
        [-16.5, 85.992, 38.481],
        [14.478, 153.195, 64.92],
        [14.517, 153.101, 64.92],
        [14.193, 153.049, 64.98],
        [-35.724, 140.07, 38.896],
        [-35.57, 140.043, 38.896],
        [-53.415, 86.269, 3.623],
        [-53.544, 86.092, 3.957],
        [-53.385, 86.143, 3.623],
        [-64.185, 150.232, 40.294],
        [-63.927, 150.191, 40.166],
        [-64.143, 150.407, 40.294],
        [14.541, 153.002, 64.92],
        [-53.485, 85.948, 3.957],
        [-35.603, 140.045, 38.896],
        [-64.63, 123.002, 40.636],
        [-64.63, 150.052, 40.636],
        [-64.79, 150.052, 40.844],
        [14.549, 152.9, 64.92],
        [-53.302, 85.698, 3.957],
        [-53.403, 85.816, 3.957],
        [-35.905, 141.002, 38.608],
        [-35.946, 141.002, 38.481],
        [-35.946, 140.075, 38.481],
        [-35.716, 140.064, 38.896],
        [0.736, 140.014, 3.158],
        [-35.633, 140.036, 38.819],
        [-64.364, 150.478, 40.452],
        [-64.553, 150.54, 40.636],
        [-53.184, 85.816, 3.623],
        [-35.702, 140.06, 38.896],
        [-35.684, 140.055, 38.896],
        [-64.281, 150.678, 40.452],
        [-53.268, 85.914, 3.623],
        [0.908001, 139.908, 3.158],
        [-64.611, 150.299, 40.636],
        [0.857, 139.952, 3.158],
        [-35.673, 140.039, 38.819],
        [-53.336, 86.024, 3.623],
        [-64.458, 150.769, 40.636],
        [-64.769, 150.324, 40.844],
        [-64.705, 150.589, 40.844],
        [-64.816, 150.626, 41.069],
        [-35.609, 140.025, 38.722],
        [-35.591, 140.033, 38.819],
        [1.03, 139.67, 3.158],
        [1.014, 139.736, 3.158],
        [-53.58, 86.243, 3.957],
        [-53.425, 86.398, 3.623],
        [0.988001, 139.799, 3.158],
        [-53.592, 86.398, 3.957],
        [-35.555, 140.023, 38.722],
        [0.952, 139.857, 3.158],
        [-35.661, 140.028, 38.722],
        [-64.705, 150.894, 41.069],
        [-64.601, 150.841, 40.844],
        [-52.602, 85.965, 3.158],
        [-52.637, 86.181, 3.038],
        [-35.563, 140.015, 38.608],
        [-35.684, 140.021, 38.608],
        [-35.625, 140.017, 38.608],
        [-64.329, 150.98, 40.636],
        [-64.458, 151.074, 40.844],
        [-64.168, 150.863, 40.452],
        [1.035, 139.602, 3.158],
        [-64.168, 151.168, 40.636],
        [1.23, 139.702, 3.354],
        [1.385, 139.857, 3.623],
        [1.207, 139.799, 3.354],
        [-63.232, 150.299, 40.017],
        [-63.052, 150.052, 39.998],
        [-63.191, 150.324, 40.017],
        [-35.79, 140.068, 38.819],
        [-35.78, 140.061, 38.819],
        [-35.794, 140.075, 38.819],
        [1.238, 139.602, 3.354],
        [-52.757, 86.243, 3.038],
        [1.169, 139.891, 3.354],
        [-63.354, 150.1, 40.017],
        [-63.343, 150.147, 40.017],
        [-16, 140.592, 3.957],
        [-16, 140.425, 3.623],
        [0.601999, 140.425, 3.623],
        [-65.358, 122.434, 45.948],
        [-65.324, 122.296, 45.978],
        [-52.811, 86.33, 3.038],
        [1.415, 139.731, 3.623],
        [-63.357, 150.052, 40.017],
        [1.425, 139.602, 3.623],
        [-65.358, 122.278, 45.978],
        [14.229, 71.026, 1.625],
        [-63.147, 150.343, 40.017],
        [-63.1, 150.354, 40.017],
        [-52.731, 86.22, 3.038],
        [-63.648, 150.147, 40.073],
        [-63.655, 150.052, 40.073],
        [-63.938, 150.052, 40.166],
        [-52.702, 86.202, 3.038],
        [-65.306, 122.451, 45.948],
        [-65.252, 122.456, 45.948],
        [-65.252, 122.311, 45.978],
        [-65.252, 122.59, 45.907],
        [-65.003, 122.59, 45.907],
        [-52.67, 86.189, 3.038],
        [-63.938, 123.002, 40.166],
        [-65.289, 122.308, 45.978],
        [0.601999, 140.035, 3.158],
        [0.601999, 140.238, 3.354],
        [-16, 140.075, 3.19662],
        [-63.324, 150.191, 40.017],
        [-16, 140.238, 3.354],
        [-63.626, 150.239, 40.073],
        [-63.894, 150.326, 40.166],
        [-65.003, 122.456, 45.948],
        [-52.702, 85.77, 3.354],
        [-65.003, 122.311, 45.978],
        [-52.602, 85.762, 3.354],
        [12.907, 75.345, 41.548],
        [0.799, 139.988, 3.158],
        [0.67, 140.03, 3.158],
        [-65.484, 122.954, 45.502],
        [-65.9, 71.866, 64.69],
        [-52.736, 85.986, 3.158],
        [-52.67, 85.97, 3.158],
        [-65.593, 122.893, 45.502],
        [-52.799, 85.793, 3.354],
        [11.357, 74.022, 41.548],
        [-65.003, 122.159, 45.996],
        [-65.003, 122.002, 46.003],
        [-65.776, 122.701, 45.581],
        [0.891001, 140.169, 3.354],
        [0.799, 140.207, 3.354],
        [-52.799, 86.012, 3.158],
        [14.549, 71.103, 1.625],
        [0.702, 140.23, 3.354],
        [-16.115, 85.967, 38.344],
        [-35.762, 140.055, 38.819],
        [1.052, 140.052, 3.354],
        [1.086, 140.268, 3.623],
        [0.976, 140.117, 3.354],
        [-16.03, 85.936, 38.344],
        [0.976, 140.336, 3.623],
        [-16.03, 85.948, 38.199],
        [-16.006, 85.925, 38.199],
        [-16.012, 85.937, 38.199],
        [-35.854, 140.075, 38.722],
        [-35.836, 140.059, 38.722],
        [-16.164, 85.975, 38.344],
        [-63.841, 150.454, 40.166],
        [-63.769, 150.573, 40.166],
        [-63.98, 150.726, 40.294],
        [11.324, 74.231, 40.844],
        [11.299, 74.389, 40.636],
        [11.052, 74.21, 40.844],
        [11.052, 74.37, 40.636],
        [-35.738, 140.049, 38.819],
        [-64.074, 150.573, 40.294],
        [-16.1, 85.969, 38.199],
        [1.117, 139.976, 3.354],
        [0.857, 140.385, 3.623],
        [0.731001, 140.415, 3.623],
        [-35.708, 140.044, 38.819],
        [-63.863, 150.863, 40.294],
        [-63.589, 150.326, 40.073],
        [-35.708, 140.032, 38.722],
        [-35.786, 140.044, 38.722],
        [-35.75, 140.037, 38.722],
        [-35.815, 140.051, 38.722],
        [-63.54, 150.407, 40.073],
        [-63.54, 150.407, 40.073],
        [-63.54, 150.407, 40.073],
        [1.184, 140.184, 3.623],
        [1.184, 140.403, 3.957],
        [-35.86, 140.047, 38.608],
        [-66.842, 71.252, 1.371],
        [-35.849, 140.067, 38.722],
        [-53.238, 139.602, 3.354],
        [-63.268, 150.268, 40.017],
        [-53.968, 86.181, 5.76],
        [-53.934, 85.965, 6.273],
        [-53.918, 85.97, 5.76],
        [-35.9, 140.066, 38.608],
        [-63.299, 150.232, 40.017],
        [1.336, 139.976, 3.623],
        [1.485, 140.052, 3.957],
        [1.403, 140.184, 3.957],
        [1.268, 140.086, 3.623],
        [-54.003, 86.398, 39.998],
        [-53.985, 86.179, 39.998],
        [-54.003, 86.398, 6.273],
        [1.302, 140.302, 3.957],
        [-65.358, 122.278, 36.022],
        [11.478, 74.636, 40.452],
        [11.407, 74.857, 40.294],
        [11.268, 74.586, 40.452],
        [-63.478, 150.478, 40.073],
        [-35.827, 140.039, 38.608],
        [-65.757, 122.675, 45.657],
        [-65.672, 122.772, 45.657],
        [-35.885, 140.056, 38.608],
        [-53.985, 86.179, 6.273],
        [-35.905, 140.075, 38.608],
        [-35.638, 140.011, 38.481],
        [-35.57, 140.009, 38.481],
        [-53.985, 86.398, 5.76],
        [-53.934, 86.398, 5.261],
        [11.232, 74.815, 40.294],
        [11.052, 74.569, 40.452],
        [11.052, 74.801, 40.294],
        [-53.918, 86.189, 5.261],
        [-53.869, 85.986, 5.261],
        [14.212, 153.002, 64.98],
        [-63.407, 150.54, 40.073],
        [-16.006, 84.997, 38.199],
        [-63.147, 150.648, 40.073],
        [-63.052, 150.655, 40.073],
        [-63.052, 150.357, 40.017],
        [11.54, 74.447, 40.636],
        [14.093, 153.166, 64.98],
        [14.049, 153.193, 64.98],
        [14.132, 153.132, 64.98],
        [-16.095, 85.969, 38.05],
        [-16.06, 85.959, 38.199],
        [-35.5, 140.008, 38.481],
        [14.166, 153.093, 64.98],
        [-63.326, 150.589, 40.073],
        [13.951, 153.224, 64.98],
        [13.9, 153.229, 64.98],
        [-63.678, 150.678, 40.166],
        [14.002, 153.212, 64.98],
        [-16.151, 85.977, 38.199],
        [-16.21, 85.985, 38.199],
        [-35.702, 140.015, 38.481],
        [-35.647, 140.007, 38.344],
        [-63.239, 150.626, 40.073],
        [11.589, 74.295, 40.844],
        [-35.738, 140.026, 38.608],
        [-35.786, 140.032, 38.608],
        [-16.024, 85.948, 38.05],
        [-16.006, 85.937, 38.05],
        [14.224, 152.951, 64.98],
        [11.052, 75.062, 40.166],
        [11.147, 75.352, 40.073],
        [11.052, 75.345, 40.073],
        [11.191, 75.073, 40.166],
        [-63.573, 150.769, 40.166],
        [14.229, 152.9, 64.98],
        [-35.762, 140.021, 38.481],
        [-63.052, 75.062, 40.166],
        [-16.054, 85.959, 38.05],
        [11.573, 74.926, 40.294],
        [11.573, 75.231, 40.166],
        [11.454, 75.159, 40.166],
        [-64.027, 151.027, 40.452],
        [-35.86, 140.036, 38.481],
        [-63.726, 150.98, 40.294],
        [11.326, 75.106, 40.166],
        [11.326, 75.411, 40.073],
        [11.239, 75.374, 40.073],
        [-35.924, 140.054, 38.481],
        [-35.94, 140.065, 38.481],
        [-53.85, 86.398, 4.786],
        [-35.815, 140.028, 38.481],
        [-35.78, 140.017, 38.344],
        [-63.678, 151.281, 40.452],
        [-63.863, 151.168, 40.452],
        [-16.024, 84.997, 38.344],
        [-53.68, 86.048, 4.348],
        [-53.721, 86.22, 4.348],
        [-53.612, 85.883, 4.348],
        [11.678, 74.719, 40.452],
        [15.771, 153.853, 1.625],
        [11.1, 75.646, 40.017],
        [11.052, 75.643, 40.017],
        [11.147, 75.657, 40.017],
        [-63.326, 150.894, 40.166],
        [-63.191, 150.927, 40.166],
        [-53.735, 86.398, 4.348],
        [-65.645, 122.723, 45.729],
        [-63.454, 150.841, 40.166],
        [-16.276, 85.991, 38.199],
        [-16.284, 85.989, 38.344],
        [11.938, 151.79, 41.548],
        [-65.609, 122.657, 45.796],
        [-65.725, 122.632, 45.729],
        [11.357, 151.978, 41.548],
        [-53.835, 86.202, 4.786],
        [14.853, 154.771, 1.625],
        [14.549, 154.897, 1.625],
        [15.134, 154.599, 1.625],
        [-63.573, 151.074, 40.294],
        [-65.688, 122.802, 45.581],
        [-65.576, 122.85, 45.657],
        [-63.407, 151.143, 40.294],
        [-63.232, 151.185, 40.294],
        [11.191, 75.676, 40.017],
        [-63.478, 151.364, 40.452],
        [12.431, 151.431, 41.548],
        [0.757, 140.58, 3.957],
        [0.601999, 140.592, 3.957],
        [-53.789, 86.012, 4.786],
        [1.117, 140.612, 4.348],
        [1.268, 140.519, 4.348],
        [11.54, 75.593, 40.073],
        [11.54, 75.593, 40.073],
        [11.478, 75.522, 40.073],
        [1.052, 140.485, 3.957],
        [11.54, 75.593, 40.073],
        [-66.549, 71.103, 1.625],
        [-66.229, 71.026, 1.625],
        [-53.85, 85.762, 6.273],
        [-53.835, 85.77, 5.76],
        [-65.528, 122.723, 45.796],
        [-63.052, 150.938, 40.166],
        [0.908001, 140.544, 3.957],
        [11.407, 75.46, 40.073],
        [11.268, 75.732, 40.017],
        [-65.556, 122.796, 45.729],
        [-64.281, 151.281, 40.844],
        [11.354, 75.9, 40.017],
        [11.343, 75.853, 40.017],
        [11.626, 75.761, 40.073],
        [-53.789, 85.793, 5.261],
        [11.052, 75.948, 39.998],
        [-65.493, 122.632, 45.856],
        [-65.416, 122.675, 45.856],
        [-65.44, 122.772, 45.796],
        [1.519, 140.268, 4.348],
        [11.299, 75.768, 40.017],
        [-65.389, 122.561, 45.907],
        [1.58, 139.757, 3.957],
        [1.592, 139.602, 3.957],
        [1.544, 139.908, 3.957],
        [-65.452, 122.526, 45.907],
        [-64.074, 151.458, 40.844],
        [-63.98, 151.329, 40.636],
        [11.232, 75.701, 40.017],
        [-63.769, 151.458, 40.636],
        [-53.85, 85.762, 39.998],
        [-16, 140.735, 4.348],
        [-53.735, 85.575, 39.998],
        [0.601999, 140.735, 4.348],
        [0.601999, 140.85, 4.786],
        [-65.481, 122.942, 45.581],
        [11.324, 75.809, 40.017],
        [-35.897, 140.045, 38.481],
        [11.589, 75.674, 40.073],
        [-65.589, 122.883, 45.581],
        [-53.592, 139.602, 3.957],
        [0.952, 140.68, 4.348],
        [0.780001, 140.721, 4.348],
        [11.648, 75.853, 40.073],
        [11.894, 75.674, 40.166],
        [11.927, 75.809, 40.166],
        [-53.592, 85.408, 39.998],
        [1.403, 140.403, 4.348],
        [11.357, 75.948, 40.017],
        [-65.473, 122.907, 45.657],
        [-65.364, 122.942, 45.657],
        [1.336, 140.612, 4.786],
        [-65.459, 122.85, 45.729],
        [0.601999, 140.934, 5.261],
        [-16, 140.85, 4.786],
        [-35.994, 141.002, 38.199],
        [-35.994, 140.075, 38.199],
        [-35.976, 141.002, 38.344],
        [-35.976, 140.075, 38.344],
        [-35.574, 140.005, 38.344],
        [-35.577, 140.002, 38.199],
        [-35.653, 140.005, 38.199],
        [-63.841, 151.601, 40.844],
        [-65.321, 122.583, 45.907],
        [-65.335, 122.701, 45.856],
        [11.655, 102.997, 40.073],
        [11.655, 75.948, 40.073],
        [-35.5, 140, 38.05],
        [-54.003, 139.602, 6.273],
        [-35.578, 140.001, 38.05],
        [-63.894, 151.705, 41.069],
        [-53.934, 85.965, 39.998],
        [-65.252, 122.71, 45.856],
        [-65.003, 122.71, 45.856],
        [-64.143, 151.553, 41.069],
        [-63.54, 151.553, 40.636],
        [0.798, 140.835, 4.786],
        [11.354, 150.1, 40.017],
        [11.052, 150.052, 39.998],
        [11.357, 150.052, 40.017],
        [-35.924, 140.043, 38.344],
        [-35.885, 140.033, 38.344],
        [11.343, 150.147, 40.017],
        [-16.353, 85.993, 38.344],
        [-16.426, 85.995, 38.344],
        [0.988001, 140.789, 4.786],
        [11.299, 150.232, 40.017],
        [11.324, 150.191, 40.017],
        [-53.85, 139.602, 4.786],
        [-63.268, 151.414, 40.452],
        [-16.347, 85.995, 38.199],
        [11.648, 150.147, 40.073],
        [11.655, 150.052, 40.073],
        [11.938, 150.052, 40.166],
        [-35.716, 140.011, 38.344],
        [-35.836, 140.025, 38.344],
        [-63.052, 151.199, 40.294],
        [-53.035, 85.066, 39.998],
        [1.169, 140.714, 4.786],
        [11.1, 150.354, 40.017],
        [11.147, 150.343, 40.017],
        [11.052, 150.357, 40.017],
        [-16.422, 85.999, 38.05],
        [-16.423, 85.998, 38.199],
        [-35.9, 140.031, 38.199],
        [-63.052, 151.431, 40.452],
        [-35.94, 140.041, 38.199],
        [-63.589, 151.705, 40.844],
        [-63.052, 151.63, 40.636],
        [-63.299, 151.611, 40.636],
        [-35.724, 140.009, 38.199],
        [-16.273, 85.992, 38.05],
        [-16.345, 85.996, 38.05],
        [-35.994, 85.937, 3.18503],
        [11.191, 150.324, 40.017],
        [-16.146, 85.978, 38.05],
        [-35.849, 140.023, 38.199],
        [-63.324, 151.769, 40.844],
        [-65.252, 122.99, 45.581],
        [-65.368, 122.978, 45.581],
        [-35.79, 140.015, 38.199],
        [-16.206, 85.986, 38.05],
        [11.147, 150.648, 40.073],
        [1.207, 140.789, 5.261],
        [11.052, 150.655, 40.073],
        [11.326, 150.589, 40.073],
        [-65.357, 122.883, 45.729],
        [-65.003, 122.954, 45.657],
        [-65.252, 122.954, 45.657],
        [-35.854, 140.022, 38.05],
        [11.268, 150.268, 40.017],
        [-35.905, 140.031, 38.05],
        [11.232, 150.299, 40.017],
        [-65.003, 123.002, 45.502],
        [-16.5, 85.999, 38.199],
        [-16.5, 85.996, 38.344],
        [-65.347, 122.802, 45.796],
        [-65.252, 122.893, 45.729],
        [-35.946, 140.041, 38.05],
        [-35.97, 140.052, 38.199],
        [11.407, 150.54, 40.073],
        [11.407, 150.54, 40.073],
        [-35.727, 140.008, 38.05],
        [-35.655, 140.004, 38.05],
        [-65.003, 122.893, 45.729],
        [-35.239, 109.173, 2.998],
        [-35.569, 110.097, 2.998],
        [11.769, 74.542, 40.636],
        [11.863, 74.832, 40.452],
        [11.98, 74.671, 40.636],
        [-35.794, 140.014, 38.05],
        [-65.252, 122.811, 45.796],
        [1.23, 140.835, 5.76],
        [1.03, 140.918, 5.76],
        [11.841, 74.399, 40.844],
        [-65.003, 122.99, 45.581],
        [-65.003, 122.811, 45.796],
        [12.074, 74.542, 40.844],
        [12.168, 74.832, 40.636],
        [-63.343, 151.884, 41.069],
        [12.281, 74.719, 40.844],
        [-63.626, 151.816, 41.069],
        [-35.988, 140.063, 38.199],
        [-35.97, 140.064, 38.344],
        [1.415, 140.721, 5.76],
        [1.385, 140.68, 5.261],
        [-35.952, 140.053, 38.344],
        [-54.003, 102.997, 27.0025],
        [-54.003, 123.002, 27.0025],
        [-65.003, 123.002, 41.548],
        [-16, 140.934, 5.261],
        [12.143, 74.447, 41.069],
        [12.364, 74.636, 41.069],
        [-63.052, 151.79, 40.844],
        [1.544, 140.544, 5.261],
        [11.678, 75.322, 40.166],
        [-64.978, 123.002, 41.305],
        [-64.978, 150.052, 41.305],
        [-65.003, 150.052, 41.548],
        [11.54, 150.407, 40.073],
        [-64.907, 123.002, 41.069],
        [-66.003, 115.988, 39.864],
        [-66.003, 115.999, 39.834],
        [-64.907, 150.052, 41.069],
        [-66.003, 116.002, 36.498],
        [-66.003, 116.002, 39.802],
        [-35.994, 140.063, 38.05],
        [11.626, 74.184, 41.069],
        [-35.976, 140.052, 38.05],
        [0.819, 140.968, 5.76],
        [1.014, 140.869, 5.261],
        [0.811001, 140.918, 5.261],
        [11.589, 150.326, 40.073],
        [11.726, 75.02, 40.294],
        [-35.655, 140.004, 3.14062],
        [-64.884, 150.343, 41.069],
        [-35.727, 140.008, 3.14286],
        [11.863, 75.137, 40.294],
        [-16.095, 140.031, 3.15576],
        [-16.0786, 140.035, 3.158],
        [-64.955, 150.354, 41.305],
        [11.626, 150.239, 40.073],
        [12.027, 74.973, 40.452],
        [11.98, 75.274, 40.294],
        [-64.553, 151.143, 41.069],
        [12.168, 75.137, 40.452],
        [0.601999, 140.985, 5.76],
        [-64.884, 150.648, 41.305],
        [-64.769, 150.927, 41.305],
        [-16, 140.985, 5.76],
        [-16.422, 140.001, 3.13893],
        [-16.345, 140.004, 3.14062],
        [-16, 141.002, 6.273],
        [11.841, 150.454, 40.166],
        [-64.978, 150.357, 41.548],
        [11.239, 150.626, 40.073],
        [-65.252, 115.702, 35.998],
        [-65.252, 110.298, 35.998],
        [12.329, 75.02, 40.636],
        [-64.364, 151.364, 41.069],
        [12.281, 75.322, 40.452],
        [1.85, 139.602, 4.786],
        [12.458, 75.231, 40.636],
        [-16.146, 140.022, 3.15071],
        [11.407, 150.54, 40.073],
        [11.478, 150.478, 40.073],
        [-68, 116.002, 36.198],
        [-64.611, 151.185, 41.305],
        [11.326, 150.894, 40.166],
        [-64.79, 150.938, 41.548],
        [12.458, 74.926, 40.844],
        [12.601, 75.159, 40.844],
        [11.938, 75.948, 40.166],
        [12.185, 75.768, 40.294],
        [-66.093, 72.834, 64.98],
        [-66.132, 72.868, 64.98],
        [-16.5, 140, 3.13837],
        [-64.63, 151.199, 41.548],
        [-53.735, 139.602, 4.348],
        [-65.9, 72.771, 64.98],
        [-65.9, 72.451, 64.92],
        [-64.907, 150.655, 41.548],
        [11.841, 75.546, 40.166],
        [-53.985, 139.602, 5.76],
        [-65.9, 152.9, -3.17524e-14],
        [-65.9, 73.1, -3.17524e-14],
        [-66.229, 152.9, 0.02],
        [-16.024, 140.052, 3.17441],
        [-16.006, 140.063, 3.18503],
        [-16.054, 140.041, 3.16379],
        [12.074, 75.427, 40.294],
        [11.769, 75.427, 40.166],
        [1.735, 139.602, 4.348],
        [1.835, 139.798, 4.786],
        [1.721, 139.78, 4.348],
        [12.143, 75.593, 40.294],
        [-65.951, 72.776, 64.98],
        [-66.002, 72.788, 64.98],
        [-66.049, 72.807, 64.98],
        [1.485, 140.485, 4.786],
        [1.612, 140.336, 4.786],
        [11.191, 150.927, 40.166],
        [-16.273, 140.008, 3.14286],
        [11.052, 150.938, 40.166],
        [11.052, 151.199, 40.294],
        [11.232, 151.185, 40.294],
        [-35.905, 140.031, 3.15576],
        [-66.002, 72.459, 64.92],
        [-66.101, 72.483, 64.92],
        [11.573, 150.769, 40.166],
        [11.454, 150.841, 40.166],
        [-66.281, 72.575, 64.92],
        [12.364, 75.522, 40.452],
        [-35.946, 140.041, 3.16379],
        [-35.976, 140.052, 3.17441],
        [1.68, 139.952, 4.348],
        [1.714, 140.169, 4.786],
        [1.612, 140.117, 4.348],
        [12.414, 75.732, 40.452],
        [11.407, 151.143, 40.294],
        [-66.049, 72.158, 64.823],
        [12.553, 75.46, 40.636],
        [1.789, 139.988, 4.786],
        [12.611, 75.701, 40.636],
        [-16.206, 84.997, 38.819],
        [12.705, 75.411, 40.844],
        [12.769, 75.676, 40.844],
        [11.573, 151.074, 40.294],
        [-35.794, 140.014, 3.14622],
        [-16.206, 85.986, 3.14622],
        [-65.9, 72.147, 64.823],
        [-35.578, 140.001, 3.13893],
        [-35.854, 140.022, 3.15071],
        [1.968, 139.819, 5.76],
        [1.985, 139.821, 6.273],
        [-35.994, 140.063, 3.18503],
        [-16.095, 84.997, 38.608],
        [11.726, 150.98, 40.294],
        [2.003, 139.602, 6.273],
        [12.431, 75.948, 40.452],
        [12.63, 75.948, 40.636],
        [1.934, 139.602, 5.261],
        [1.918, 139.811, 5.261],
        [-64.414, 151.414, 41.305],
        [12.199, 75.948, 40.294],
        [-66.093, 71.881, 64.69],
        [1.869, 140.014, 5.261],
        [-64.431, 151.431, 41.548],
        [-16.273, 85.992, 3.14286],
        [1.85, 140.238, 6.273],
        [1.835, 140.23, 5.76],
        [1.918, 140.03, 5.76],
        [-16.146, 85.978, 3.15071],
        [12.79, 75.948, 40.844],
        [-35.5, 140, 3.13837],
        [12.431, 102.997, 40.452],
        [12.63, 102.997, 40.636],
        [1.721, 140.415, 5.76],
        [1.58, 140.58, 5.76],
        [1.68, 140.385, 5.261],
        [11.938, 102.997, 40.166],
        [-64.185, 151.611, 41.305],
        [-64.199, 151.63, 41.548],
        [12.816, 75.374, 41.069],
        [-35.536, 85.959, 38.896],
        [11.343, 74.116, 41.069],
        [-35.5, 85.999, 38.199],
        [1.789, 140.207, 5.261],
        [11.052, 74.093, 41.069],
        [-65.9, 71.401, 64.33],
        [-66.132, 71.633, 64.524],
        [-66.166, 71.422, 64.33],
        [11.052, 74.022, 41.305],
        [11.354, 74.045, 41.305],
        [11.648, 74.116, 41.305],
        [-65.9, 71.615, 64.524],
        [-63.648, 151.884, 41.305],
        [-63.927, 151.769, 41.305],
        [-63.052, 151.907, 41.069],
        [-63.052, 151.978, 41.305],
        [-65.9, 71.229, 64.113],
        [-63.354, 151.955, 41.305],
        [11.655, 74.093, 41.548],
        [12.431, 150.052, 40.452],
        [12.431, 123.002, 40.452],
        [12.199, 150.052, 40.294],
        [1.238, 140.85, 39.998],
        [1.238, 140.85, 6.273],
        [1.425, 140.735, 6.273],
        [11.052, 73.997, 41.548],
        [-35.5, 85.986, 38.608],
        [-63.655, 151.907, 41.548],
        [-65.9, 71.103, 63.877],
        [11.894, 74.295, 41.069],
        [1.035, 140.934, 6.273],
        [11.927, 74.231, 41.305],
        [1.035, 140.934, 39.998],
        [0.820999, 140.985, 6.273],
        [0.601999, 141.002, 6.273],
        [12.185, 74.389, 41.305],
        [11.938, 74.21, 41.548],
        [-52.821, 139.602, 3.038],
        [-35.524, 85.948, 38.954],
        [-35.512, 85.937, 38.988],
        [-53.035, 139.602, 3.158],
        [-35.5, 85.978, 38.722],
        [-35.5, 85.969, 38.819],
        [12.553, 74.857, 41.069],
        [12.705, 75.106, 41.069],
        [-35.5, 85.996, 38.344],
        [-63.052, 152.003, 41.548],
        [12.199, 74.37, 41.548],
        [1.592, 140.592, 6.273],
        [1.934, 140.035, 6.273],
        [12.414, 74.586, 41.305],
        [-35.546, 85.934, 38.988],
        [-35.555, 85.933, 38.988],
        [-35.536, 85.935, 38.988],
        [1.735, 140.425, 6.273],
        [-35.524, 85.936, 38.988],
        [12.611, 74.815, 41.305],
        [-35.548, 85.947, 38.954],
        [1.592, 140.592, 39.998],
        [1.425, 140.735, 39.998],
        [12.769, 75.073, 41.305],
        [12.63, 74.801, 41.548],
        [11.052, 152.003, 41.548],
        [-35.577, 85.927, 38.988],
        [-35.578, 85.925, 38.988],
        [-35.574, 85.929, 38.988],
        [1.985, 139.821, 39.998],
        [11.678, 150.678, 40.166],
        [-35.57, 85.93, 38.988],
        [-35.563, 85.932, 38.988],
        [12.79, 150.052, 40.844],
        [12.63, 150.052, 40.636],
        [-35.57, 85.957, 38.896],
        [12.431, 74.569, 41.548],
        [-22.998, 140, 8.802],
        [-22.998, 155, 8.802],
        [-22.998, 155, 5.198],
        [11.894, 150.326, 40.166],
        [11.769, 150.573, 40.166],
        [12.884, 75.352, 41.305],
        [-22.998, 140, 5.198],
        [-35.591, 85.944, 38.954],
        [-35.609, 85.941, 38.954],
        [-28.702, 155, 9.003],
        [-23.298, 140, 9.003],
        [-28.702, 140, 9.003],
        [-35.57, 85.946, 38.954],
        [-35.653, 85.929, 38.954],
        [-35.9214, 140.035, 3.158],
        [13.9, 154.974, 1.371],
        [-65.9, 154.897, 1.123],
        [-65.9, 154.974, 1.371],
        [-29.003, 155, 1.625],
        [12.79, 75.062, 41.548],
        [-35.638, 85.936, 38.954],
        [-29.003, 140, 5.198],
        [11.927, 150.191, 40.166],
        [-35.647, 85.932, 38.954],
        [-23.298, 140, 4.998],
        [12.884, 75.657, 41.069],
        [-35.661, 85.949, 38.896],
        [12.907, 75.948, 41.069],
        [12.79, 102.997, 40.844],
        [-66.224, 154.949, 1.371],
        [-35.603, 85.955, 38.896],
        [-35.655, 85.925, 38.954],
        [12.074, 150.573, 40.294],
        [-52.602, 139.602, 2.998],
        [1.934, 140.035, 39.998],
        [12.143, 150.407, 40.294],
        [12.364, 150.478, 40.452],
        [-66.224, 71.051, 63.629],
        [-66.229, 71.026, 63.375],
        [-65.9, 71.026, 63.629],
        [-35.625, 85.939, 38.954],
        [12.414, 150.268, 40.452],
        [-52.602, 140.035, 3.158],
        [-64.978, 75.643, 41.548],
        [-35.724, 85.93, 38.896],
        [12.281, 150.678, 40.452],
        [12.185, 150.232, 40.294],
        [1.735, 140.425, 39.998],
        [12.978, 75.948, 41.305],
        [12.955, 75.646, 41.305],
        [0.820999, 140.985, 39.998],
        [-66.224, 73.049, 64.98],
        [-52.602, 139.821, 3.038],
        [-16.048, 112.02, 2.998],
        [-16.192, 111.049, 2.998],
        [-16, 113, 2.998],
        [2.003, 123.002, 27.0025],
        [4.003, 123.002, 30],
        [2.003, 123.002, 32.9985],
        [-35.655, 84.997, 38.954],
        [-35.578, 84.997, 38.988],
        [-24.04, 119.462, 15],
        [-24.244, 121.827, 15],
        [-24.683, 119.623, 15],
        [-21.757, 120.937, 15],
        [-22.556, 121.315, 15],
        [-22.817, 118.955, 15],
        [-66.541, 72.998, 64.92],
        [-66.517, 72.899, 64.92],
        [-35.555, 85.977, 38.722],
        [-35.546, 85.969, 38.819],
        [-21, 120.483, 15],
        [-21.716, 118.22, 15],
        [-20.29, 119.957, 15],
        [-66.166, 72.907, 64.98],
        [-66.193, 72.951, 64.98],
        [-66.212, 72.998, 64.98],
        [-19.28, 112.338, 15],
        [-19.377, 111.683, 15],
        [-17.043, 112.118, 15],
        [-53.23, 139.702, 3.354],
        [-53.03, 139.67, 3.158],
        [-53.014, 139.736, 3.158],
        [-22.249, 118.614, 15],
        [-23.416, 119.238, 15],
        [-25.118, 121.957, 15],
        [-23.387, 121.612, 15],
        [-35.633, 85.953, 38.896],
        [-21.225, 117.775, 15],
        [-19.636, 119.364, 15],
        [-35.591, 85.967, 38.819],
        [2.003, 103.689, 36.022],
        [2.003, 103.841, 36.004],
        [2.003, 103.41, 36.093],
        [2.003, 103.544, 36.052],
        [2.003, 103.046, 36.343],
        [-66.425, 72.719, 64.92],
        [-19.762, 110.416, 15],
        [-17.685, 109.556, 15],
        [-19.538, 111.04, 15],
        [-35.684, 85.945, 38.896],
        [2.003, 103.107, 36.271],
        [2.003, 103.189, 36.204],
        [2.003, 103.29, 36.144],
        [-19.248, 113, 15],
        [-17, 113, 15],
        [-19.28, 113.662, 15],
        [-35.702, 85.94, 38.896],
        [-17.685, 116.444, 15],
        [-19.538, 114.96, 15],
        [-17.388, 115.613, 15],
        [13.003, 103.41, 45.907],
        [13.003, 103.29, 45.856],
        [-19.377, 114.317, 15],
        [-17.173, 114.756, 15],
        [13.003, 103.046, 45.657],
        [13.003, 103.107, 45.729],
        [13.003, 103.189, 45.796],
        [-20.386, 116.751, 15],
        [-20.045, 116.183, 15],
        [-18.517, 118, 15],
        [-19.762, 115.584, 15],
        [-20.78, 117.284, 15],
        [-18.063, 117.243, 15],
        [-35.738, 85.951, 38.819],
        [-19.043, 118.71, 15],
        [2.003, 103.998, 35.998],
        [13.003, 103.689, 45.978],
        [13.003, 103.841, 45.996],
        [-52.819, 139.637, 3.038],
        [-17.173, 111.244, 15],
        [-17.388, 110.387, 15],
        [-17.043, 113.882, 15],
        [-35.633, 85.964, 38.819],
        [13.003, 103.544, 45.948],
        [-27.756, 121.827, 15],
        [-27.317, 119.623, 15],
        [-26.882, 121.957, 15],
        [-66.853, 73.1, 64.823],
        [-67.134, 73.1, 64.69],
        [-67.119, 72.907, 64.69],
        [-26, 122, 15],
        [-25.338, 119.72, 15],
        [-28.584, 119.238, 15],
        [-29.444, 121.315, 15],
        [-29.183, 118.955, 15],
        [-27.96, 119.462, 15],
        [-35.673, 85.961, 38.819],
        [-52.988, 139.799, 3.158],
        [-52.798, 139.702, 3.038],
        [-52.952, 139.857, 3.158],
        [-66.842, 72.951, 64.823],
        [13.003, 103.998, 46.003],
        [-67.385, 73.1, 64.524],
        [-31.71, 119.957, 15],
        [-30.284, 118.22, 15],
        [-31, 120.483, 15],
        [-30.243, 120.937, 15],
        [-53.425, 139.602, 3.623],
        [-53.415, 139.731, 3.623],
        [-32.957, 118.71, 15],
        [-30.775, 117.775, 15],
        [-32.364, 119.364, 15],
        [-26.662, 119.72, 15],
        [-29.751, 118.614, 15],
        [-28.613, 121.612, 15],
        [-26, 119.752, 15],
        [-31.955, 116.183, 15],
        [-31.614, 116.751, 15],
        [-33.483, 118, 15],
        [-33.937, 117.243, 15],
        [-34.315, 116.444, 15],
        [-35.708, 85.968, 38.722],
        [-32.623, 114.317, 15],
        [-34.957, 113.882, 15],
        [-32.72, 113.662, 15],
        [-66.478, 72.805, 64.92],
        [-35, 113, 15],
        [-34.957, 112.118, 15],
        [-32.753, 113, 15],
        [-32.623, 111.683, 15],
        [-32.72, 112.338, 15],
        [-35.609, 85.975, 38.722],
        [-66.749, 72.667, 64.823],
        [-34.827, 114.756, 15],
        [-32.462, 114.96, 15],
        [-34.612, 115.613, 15],
        [12.978, 75.643, 41.548],
        [-32.238, 115.584, 15],
        [-31.22, 117.284, 15],
        [-66.359, 72.641, 64.92],
        [13.003, 75.948, 41.548],
        [-18.517, 108, 15],
        [-18.063, 108.757, 15],
        [-20.045, 109.817, 15],
        [-65.9, 154.385, 0.476],
        [-66.132, 154.367, 0.476],
        [-65.9, 154.599, 0.67],
        [-35.661, 85.972, 38.722],
        [-33.937, 108.757, 15],
        [-33.483, 108, 15],
        [-31.955, 109.817, 15],
        [-34.315, 109.556, 15],
        [-32.238, 110.416, 15],
        [-65.9, 154.134, 0.31],
        [-66.093, 154.119, 0.31],
        [-66.281, 154.074, 0.31],
        [-53.169, 139.891, 3.354],
        [-53.207, 139.799, 3.354],
        [-21.225, 108.225, 15],
        [-19.043, 107.29, 15],
        [-20.78, 108.716, 15],
        [-35.738, 85.974, 38.608],
        [-21.716, 107.78, 15],
        [-20.29, 106.043, 15],
        [-66.049, 153.842, 0.177],
        [-21, 105.517, 15],
        [-22.249, 107.385, 15],
        [-21.757, 105.063, 15],
        [-19.636, 106.636, 15],
        [-20.386, 109.249, 15],
        [-65.9, 153.549, 0.08],
        [-66.002, 153.541, 0.08],
        [-65.9, 153.853, 0.177],
        [-22.817, 107.045, 15],
        [-22.556, 104.685, 15],
        [-24.04, 106.538, 15],
        [-23.387, 104.388, 15],
        [-24.244, 104.173, 15],
        [-24.683, 106.377, 15],
        [-25.118, 104.043, 15],
        [-53.58, 139.757, 3.957],
        [-23.416, 106.762, 15],
        [-66.807, 72.805, 64.823],
        [-66.195, 72.522, 64.92],
        [-66.101, 153.517, 0.08],
        [-53.544, 139.908, 3.957],
        [-53.385, 139.857, 3.623],
        [-66.574, 72.426, 64.823],
        [13.481, 103.058, 45.581],
        [13.484, 103.046, 45.502],
        [13.368, 103.022, 45.581],
        [-35.684, 85.979, 38.608],
        [-53.336, 139.976, 3.623],
        [13.37, 103.01, 45.502],
        [-66.002, 153.212, 0.02],
        [-66.049, 153.193, 0.02],
        [-65.951, 153.224, 0.02],
        [13.484, 103.046, 36.498],
        [-35.563, 85.985, 38.608],
        [13.252, 103.01, 45.581],
        [13.003, 103.01, 45.581],
        [13.252, 103.046, 45.657],
        [-35.727, 85.925, 38.896],
        [-52.811, 139.67, 3.038],
        [13.364, 103.058, 45.657],
        [13.473, 103.093, 45.657],
        [-35.716, 85.936, 38.896],
        [-66.333, 72.251, 64.823],
        [-65.9, 153.229, 0.02],
        [13.003, 102.997, 45.502],
        [-67.074, 72.719, 64.69],
        [-66.093, 153.166, 0.02],
        [-66.671, 72.54, 64.823],
        [-67, 72.54, 64.69],
        [-66.132, 153.132, 0.02],
        [-66.281, 153.425, 0.08],
        [-35.708, 85.956, 38.819],
        [-25.338, 106.28, 15],
        [-27.756, 104.173, 15],
        [-26.882, 104.043, 15],
        [-27.317, 106.377, 15],
        [13.593, 103.107, 45.502],
        [13.593, 103.107, 36.498],
        [13.693, 103.189, 45.502],
        [13.693, 103.189, 36.498],
        [-66.899, 72.374, 64.69],
        [-35.794, 85.925, 38.819],
        [-30.243, 105.063, 15],
        [-29.444, 104.685, 15],
        [-29.183, 107.045, 15],
        [-28.584, 106.762, 15],
        [-27.96, 106.538, 15],
        [-35.78, 85.939, 38.819],
        [13.252, 103.189, 45.796],
        [-67.312, 72.641, 64.524],
        [-67.223, 72.426, 64.524],
        [-31, 105.517, 15],
        [-29.751, 107.385, 15],
        [-35.762, 85.945, 38.819],
        [-28.613, 104.388, 15],
        [-26.662, 106.28, 15],
        [-26, 106.247, 15],
        [-26, 104, 15],
        [-66.773, 72.227, 64.69],
        [-31.71, 106.043, 15],
        [-30.284, 107.78, 15],
        [-30.775, 108.225, 15],
        [-34.827, 111.244, 15],
        [-32.462, 111.04, 15],
        [-34.612, 110.387, 15],
        [-32.364, 106.636, 15],
        [-32.957, 107.29, 15],
        [-35.79, 85.932, 38.819],
        [-31.22, 108.716, 15],
        [-63.052, 74.21, 40.844],
        [-35.786, 85.956, 38.722],
        [-35.75, 85.962, 38.722],
        [-63.052, 74.37, 40.636],
        [13.357, 103.117, 45.729],
        [13.459, 103.15, 45.729],
        [-63.052, 74.801, 40.294],
        [-31.614, 109.249, 15],
        [-63.052, 75.643, 40.017],
        [-63.052, 75.948, 39.998],
        [-16.048, 112.02, 14.3],
        [-16.192, 111.049, 14.3],
        [-35.849, 85.933, 38.722],
        [-35.854, 85.925, 38.722],
        [-16.192, 114.951, 14.3],
        [-16.048, 113.98, 14.3],
        [-16.048, 113.98, 2.998],
        [15.897, 72.451, 1.625],
        [15.771, 72.147, 1.625],
        [-16, 113, 14.3],
        [-16.761, 116.827, 14.3],
        [-16.431, 115.903, 14.3],
        [-35.815, 85.949, 38.722],
        [15.873, 72.459, 1.371],
        [-35.836, 85.941, 38.722],
        [-16.192, 114.951, 2.998],
        [-17.685, 118.556, 2.998],
        [-17.181, 117.714, 2.998],
        [13.252, 103.107, 45.729],
        [13.347, 103.198, 45.796],
        [15.949, 72.776, 1.371],
        [15.974, 73.1, 1.371],
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
